sswegy/ANCAudioSystem/AudioSystemEQPanel/AudioSystemEQPanel.kicad_sch

## KiCad design AudioSystemEQPanel/AudioSystemEQPanel.kicad_sch (2024-10-22)

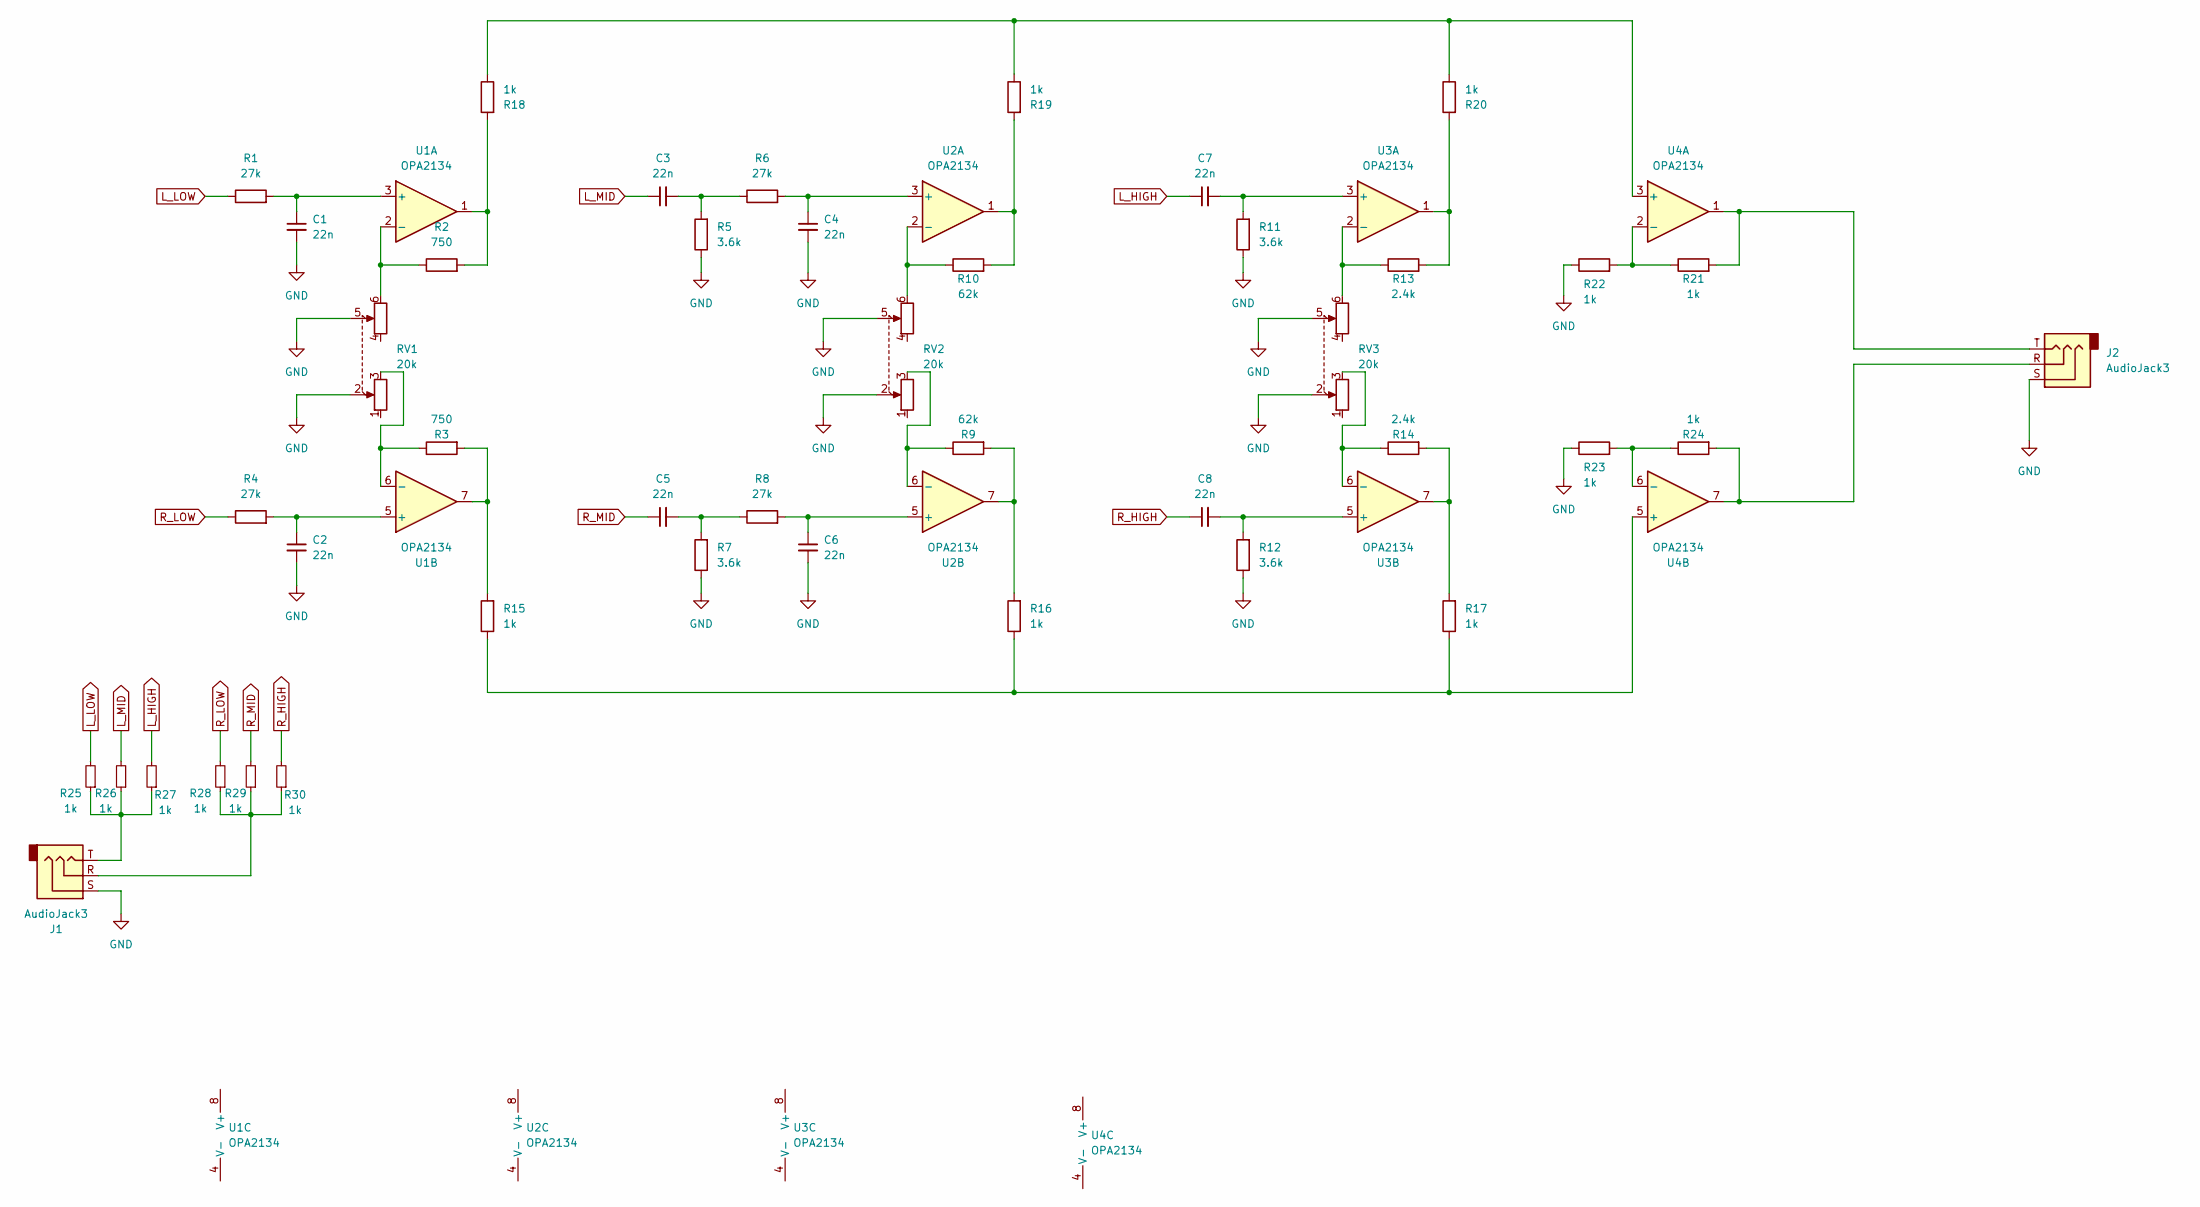
[picture p22: schematic AudioSystemEQPanel.kicad_sch]

Parts:
C1, C2, C3, C4, C5, C6, C7, C8: 22n
J1, J2: AudioJack3
R1, R4, R6, R8: 27k
R2, R3: 750
R5, R7, R11, R12: 3.6k
R9, R10: 62k
R13, R14: 2.4k
R15, R16, R17, R18, R19, R20, R21, R22, R23, R24, R25, R26, R27, R28, R29, R30: 1k
RV1, RV2, RV3: 20k
U1, U2, U3, U4: OPA2134; OPA2134UA

Connections:
GND: C1.2, C2.2, C4.2, C6.2, J1.S, J2.S, R5.1, R7.1, R11.1, R12.1, R22.1, R23.1, RV1.2, RV1.5, RV2.2, RV2.5, RV3.2, RV3.5
L_HIGH: C7.1, R27.2
L_LOW: R1.1, R25.2
L_MID: C3.1, R26.2
unnamed: C1.1, R1.2, U1.3 (+)
unnamed: C2.1, R4.2, U1.5 (+)
unnamed: C3.2, R5.2, R6.1
unnamed: C4.1, R6.2, U2.3 (+)
unnamed: C5.2, R7.2, R8.1
unnamed: C6.1, R8.2, U2.5 (+)
unnamed: C7.2, R11.2, U3.3 (+)
unnamed: C8.2, R12.2, U3.5 (+)
unnamed: J1.R, R28.1, R29.1, R30.1
unnamed: J1.T, R25.1, R26.1, R27.1
unnamed: J2.R, R24.2, U4.7
unnamed: J2.T, R21.2, U4.1
unnamed: R2.1, RV1.6, U1.2 (-)
unnamed: R3.1, RV1.3, U1.6 (-)
unnamed: R9.1, RV2.3, U2.6 (-)
unnamed: R10.1, RV2.6, U2.2 (-)
unnamed: R10.2, R19.2, U2.1
unnamed: R13.1, RV3.6, U3.2 (-)
unnamed: R13.2, R20.2, U3.1
unnamed: R14.1, RV3.3, U3.6 (-)
unnamed: R14.2, R17.2, U3.7
unnamed: R15.1, R16.1, R17.1, U4.5 (+)
unnamed: R3.2, R15.2, U1.7
unnamed: R9.2, R16.2, U2.7
unnamed: R18.1, R19.1, R20.1, U4.3 (+)
unnamed: R2.2, R18.2, U1.1
unnamed: R21.1, R22.2, U4.2 (-)
unnamed: R23.2, R24.1, U4.6 (-)
R_HIGH: C8.1, R30.2
R_LOW: R4.1, R28.2
R_MID: C5.1, R29.2
